mancio/FlyBox2/AltiumProject/componets/Arduino-PRO-MICRO-ATMEGA-32u4-Leonardo-Micro.jpg

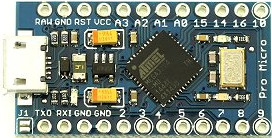
AltiumProject/componets/Arduino-PRO-MICRO-ATMEGA-32u4-Leonardo-Micro.jpg
