mancio/FlyBox2/AltiumProject/componets/multiplexer16.jpg

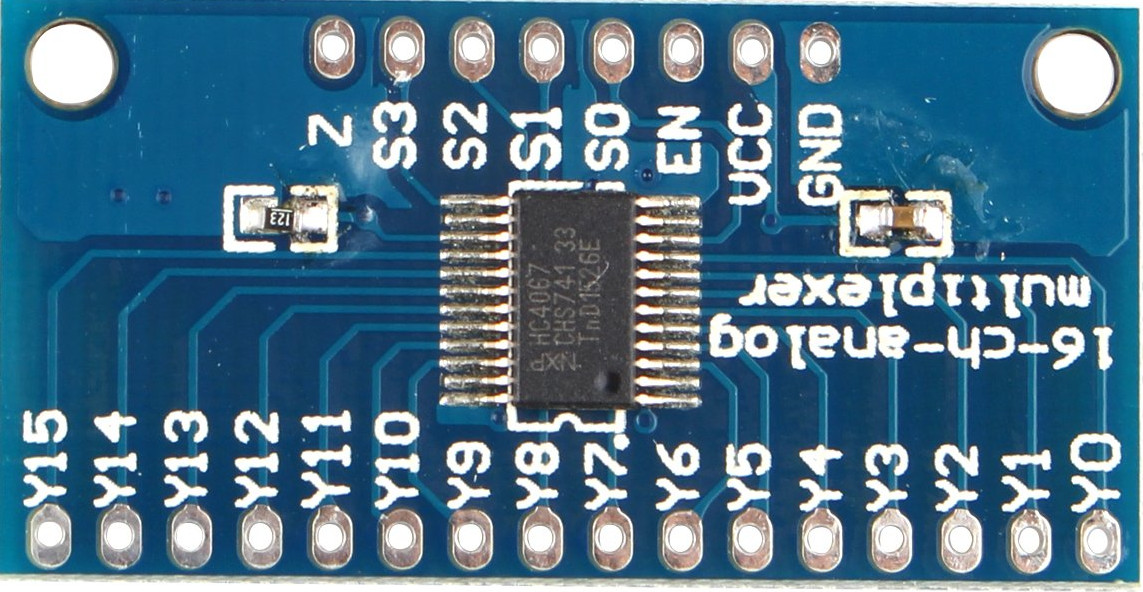
AltiumProject/componets/multiplexer16.jpg
