mancio/FlyBox2/include/Encoders.h

/*
FlyBox2 is a flight simulator game pad for games like X-plane used together 
with a joystick 

Copyright (C) 2020  Andrea Mancini

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
You should have received a copy of the GNU General Public License
along with this program.  If not, see <https://www.gnu.org/licenses/>.
*/

#ifndef ENCODER_h
#define ENCODER_h

#include <Arduino.h>
#include <Timer.h>
#include <joyconf.h>
#include <Encoder.h>


/**
 * The encoder class is used to control a classic multiturn rotary encoder
 * with click button
 * 
 * The encoder is able to sense a left or right turn thanks to two pins
 * connected to on different part of the wheel. The wheel turning pull-up or down 
 * the pins in different order.
 * 
 * The alternate LOW and HIGH state of the pins describes two squared waves 90 degrees
 * out of phase.
 *
 *   ---     ---     ---            ---     ---     ---
 *  |   |   |   |   |   |     A    |   |   |   |   |   |  
 * -     ---     ---     -        -     ---     ---     --
 * ---     ---     ---                ---     ---     ---
 *   |   |   |   |   |       B      |   |   |   |   |   | 
 *    ---     ---     ---        ---     ---    ---  
 *      Turn Left                       Turn right
 *    A 1 1 0 0 1                    A 1 1 1 0 1
 *    B 1 0 0 1 1                    B 0 1 0 0 0
 */
class Encoders_ {
    private:
        // one encoder input 
        int _clk;
        // the other encoder input
        int _dt;
        // click push button
        int _sw;

        //last encoder position
        long _last_enc_pos;
        
        // last sw state
        int _sw_last_state;

        int _sw_read;

        int _res;

        // encoder direction -1 left, 0 no move, 1 right
        int _dir;

       

        // timer class to debounce clicks
        Timer_ _Timer1;
        // timer class to debounce directions
        Timer_ _Timer2;
        // timer class to debounce directions for external inputs
        Timer_ _Timer3;

        //Encoder _MyEnc(uint8_t pina, uint8_t pinb);
        Encoder* _MyEnc;
        
    public:

        
        
        /**
         * to initialize the encoder with input pins and click pin.
         * All af them are digital inputs.
         */
        Encoders_(int clk, int dt, int sw);

       

        /**
         * give the direction (one step change)
         * 
         * @param how long time give the same output before reset to 0 output 
         * 
         * @return 1 if clockwise (right) or 0 if no changes or -1 if anticlock-wise (left)
         */
        int direction(long out_t);

        /**
         * give the direction using an external input (not encoder square wave type)
         * clk HIGH = roll left
         * dt HIGH = roll right
         * 
         * @param how long time give the same output before reset to 0 output 
         * 
         * @return 1 if clockwise (right) or 0 if no changes or -1 if anticlock-wise (left)
         */
        int ext_direction(long out_t);

        /**
         * return the SW push button state. It is debounced to avoid false clicks.
         * Please check the mechanical condition of every encoder.
         * Some encoder can need longer delay.
         * 
         * @param long deboucing time
         * 
         * @return int 0 LOW (clicked) or 1 HIGH (released).
         */ 
        int click(long deb_time);

        /**
         * return the last direction state of the encoder
         * 
         * @return int 1 (right), -1 (left).
         */ 
        int lastState();

        
};

#endif
