mancio/FlyBox2/include/joyconf.h

/*
FlyBox2 is a flight simulator game pad for games like X-plane used together 
with a joystick 

Copyright (C) 2020  Andrea Mancini

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
You should have received a copy of the GNU General Public License
along with this program.  If not, see <https://www.gnu.org/licenses/>.
*/

#ifndef JOYCONF_h
#define JOYCONF_h

// axis reverse
#define NO_REV true
#define REV false

/**
 * set the execution in test mode
 *
 * @param bool if true test mode, if false normal mode
 */
void setTest(bool testin);

/**
 * Initialize joystick library
 */
void joy_conf();

/**
 * set joystick button state according to pin input
 * 
 * @param int input pin
 * @param int button to be modified
 */
void btset(int pin, int button);

/**
 * map the potentiometer scale to the Arduino analog input scale
 * 
 * @param long input analog value from axis
 * @param bool invert axis if false 
 * 
 * @return mapped value as long
 */
long mapper(long m, bool rev);

/**
 * check and set X-axis input value
 * 
 * @param int pin number
 * @param bool if false reverse the axis
 * 
 * @return long axis value
 */
long setX(int pin, bool rev);

/**
 * check and set Y-axis input value
 * 
 * @param int pin number
 * @param bool if false reverse the axis
 * 
 * @return long axis value
 */
long setY(int pin, bool rev);

/**
 * check and set Z-axis input value
 * 
 * @param int pin number
 * @param bool if false reverse the axis
 * 
 * @return long axis value
 */
long setZ(int pin, bool rev);

/**
 * build an array of buttons in normal order 
 * from 1 to 16
 */
void btArrayFiller();

/**
 * loop the the multiplexer 16 pin connecting each of them to the SIG
 * pin and write the input on the right joystick button.
 */
void muxLooper();

/**
 * push buttons depending by encoders direction and click buttons
 */
void setEncoders_dir();



#endif
